jcsb1994/TowCam/stl_files/controller_bottom_left.stl

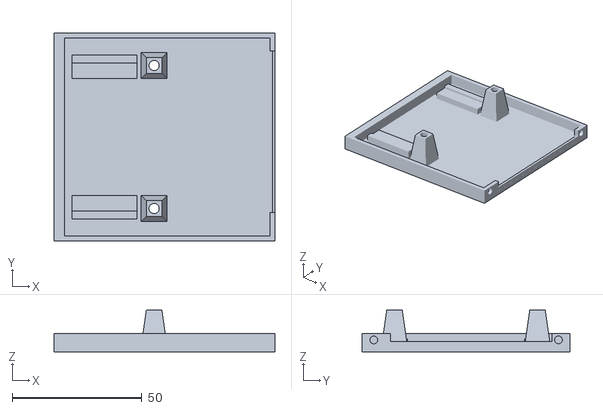
[picture p18: CAD file, 2019-01-28]
stl_files/controller_bottom_left.stl
85.0 x 80.0 x 16.0
